MirageC79/Interfaces-for-WobbleX-integration/RatRig/VCore3.1/Vcore_sliced.png

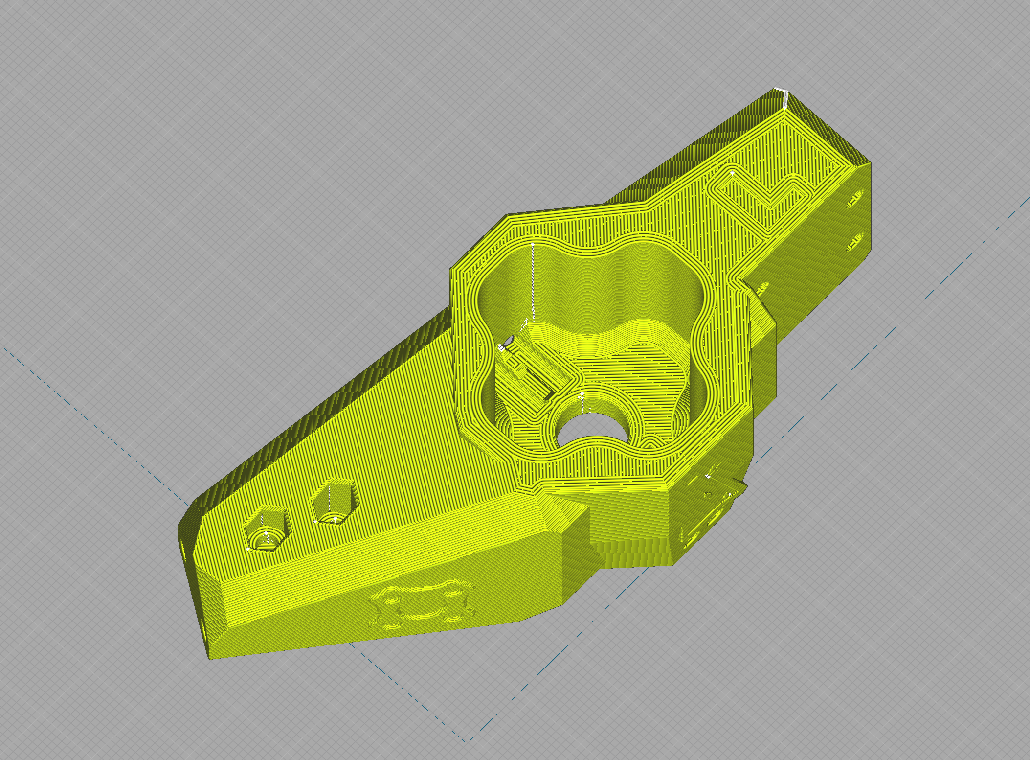
RatRig/VCore3.1/Vcore_sliced.png
