MirageC79/Interfaces-for-WobbleX-integration/RatRig/VCore3.1/Vcore_TransparentView.png

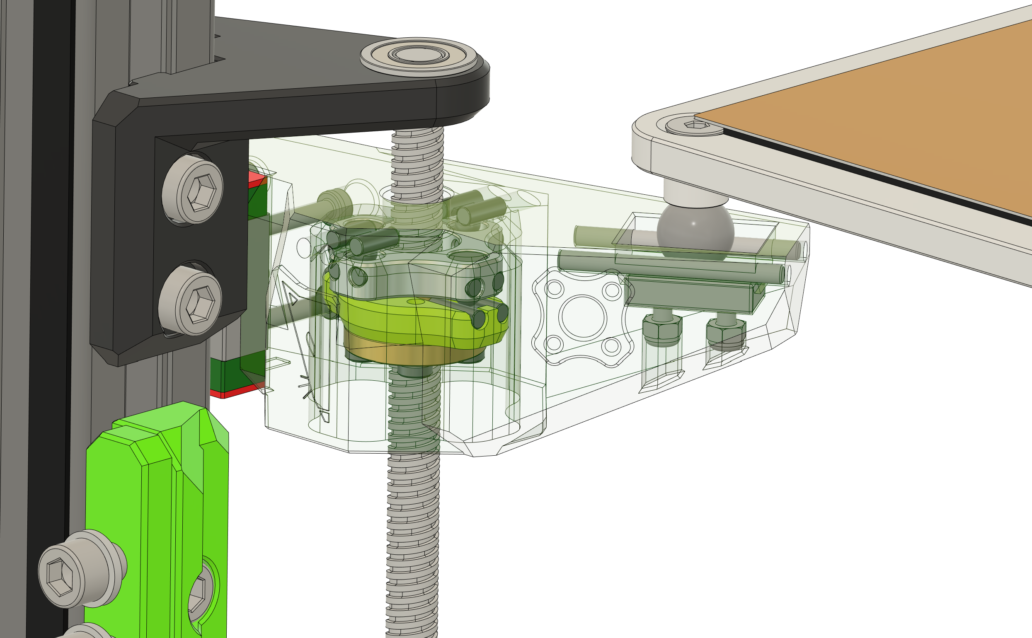
RatRig/VCore3.1/Vcore_TransparentView.png
