MirageC79/Interfaces-for-WobbleX-integration/Voron/V0.1/Voron_V0.1_WobbleX_T8_Clearance_45deg_Under.png

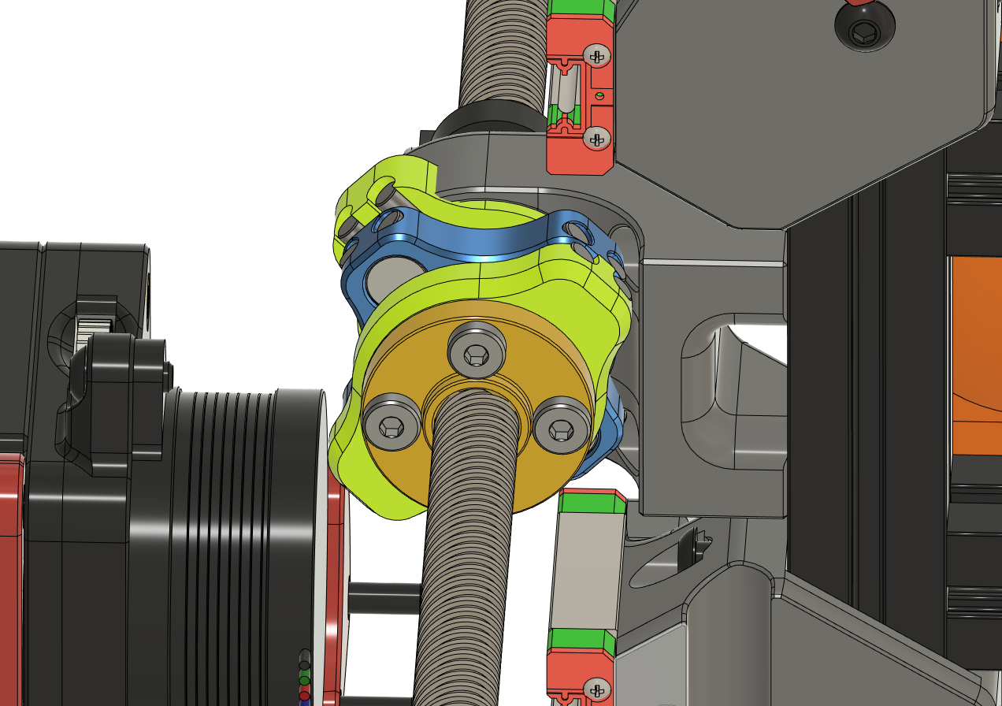
Voron/V0.1/Voron_V0.1_WobbleX_T8_Clearance_45deg_Under.png
