MirageC79/Interfaces-for-WobbleX-integration/MockUp/WobbleX_WS16_MockUp.step

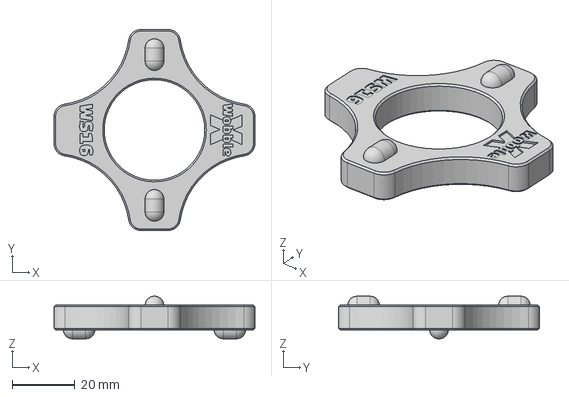
[picture p35: CAD file, 2023-03-30]
MockUp/WobbleX_WS16_MockUp.step
64.0 x 64.0 x 13.6 mm
